Olaclemmy/TSOC_GROVEY_I2CHUB/TSOC_GROVEY_I2CHUB/eagleUp/eagleUp_TSOC_GROVEY_I2CHUB_board_top.jpg

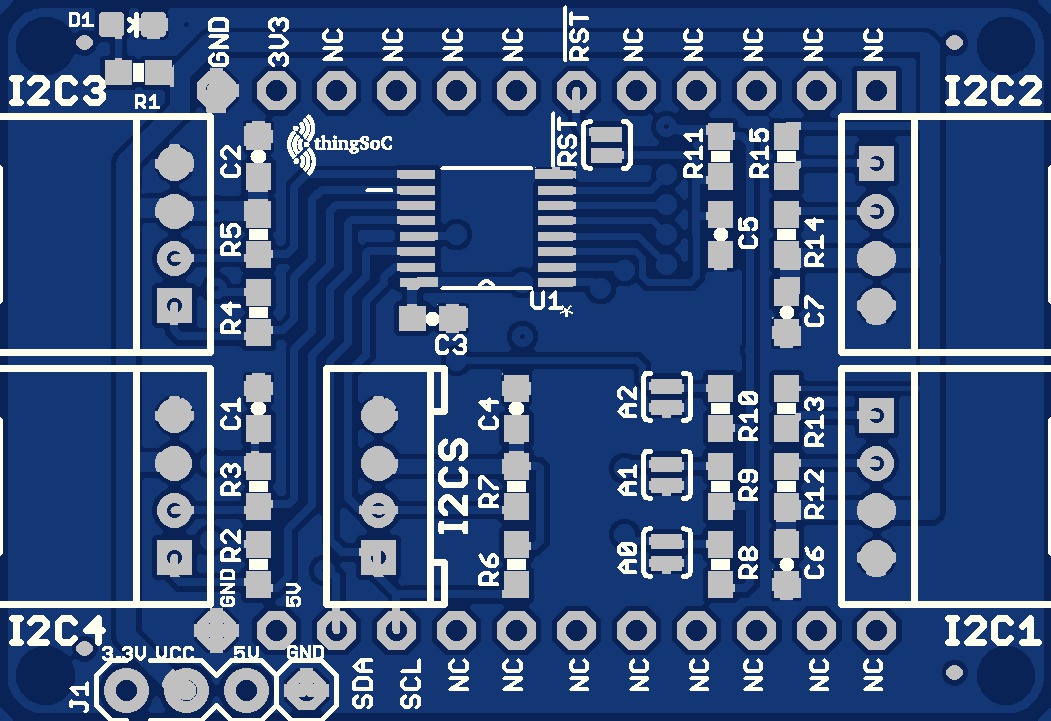
TSOC_GROVEY_I2CHUB/eagleUp/eagleUp_TSOC_GROVEY_I2CHUB_board_top.jpg
