Olaclemmy/TSOC_GROVEY_I2CHUB/TSOC_GROVEY_I2CHUB/images/product/TSOC_GROVEY_I2CHUB_from_seeed.jpg

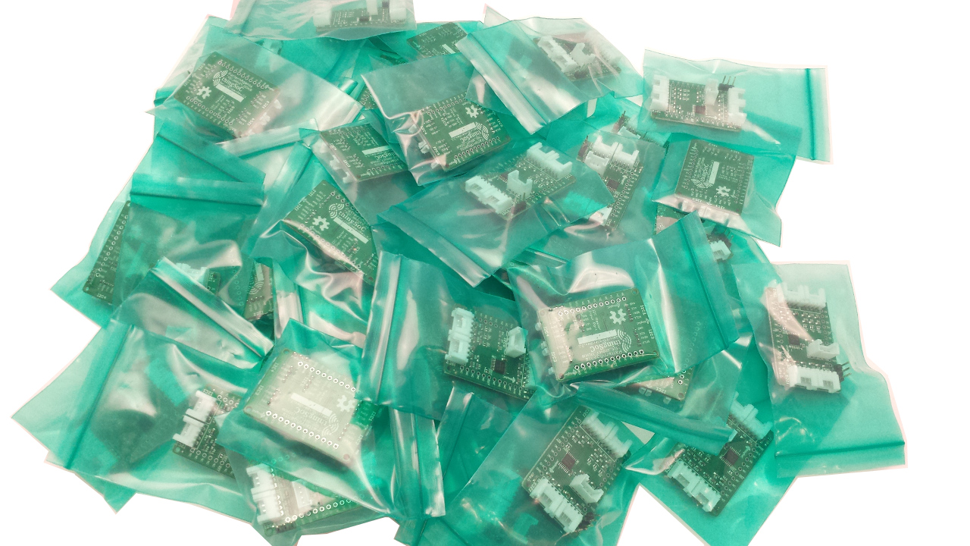
TSOC_GROVEY_I2CHUB/images/product/TSOC_GROVEY_I2CHUB_from_seeed.jpg
